htfab/tt-demo-pcb/rp2350.kicad_sch

## KiCad design rp2350.kicad_sch (2025-12-01)

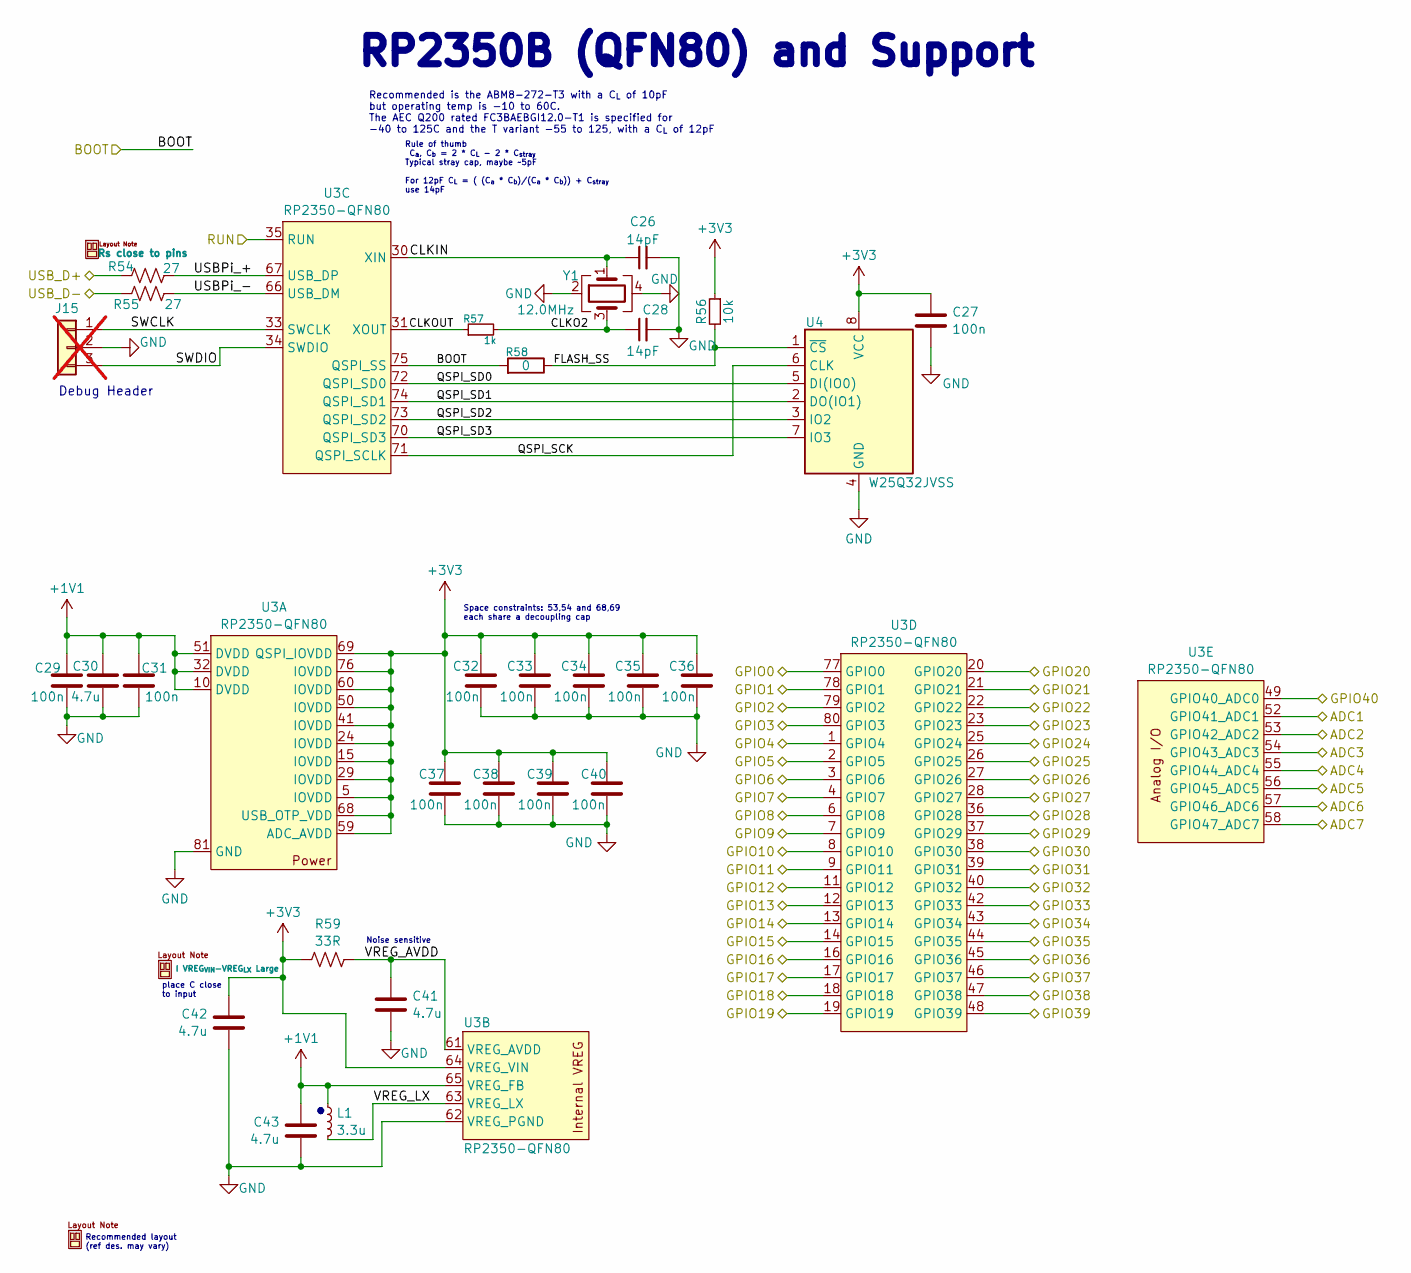
[picture p11: schematic rp2350.kicad_sch]

Parts:
C26, C28: 14pF; C_0402_1005Metric; MPN CC0402CRNPO9BN4R0; LCSC C325455
C27, C29, C31, C32, C33, C34, C35, C36, C37, C38, C39, C40: 100n; C_0402_1005Metric; MPN CL05A104KA5NNNC; LCSC C100072
C30, C41: 4.7u; C_0402_1005Metric; MPN GRM155R61E475ME15D; JLC C2858031
C42, C43: 4.7u; C_0603_1608Metric; MPN GRM188C71C475KE21D; JLC C237615
J15: Conn_01x03; PinHeader_1x03_P2.54mm_Vertical; not fitted
L1: 3.3u; L_2016X120N; MPN AOTA-B201610S3R3-101-T; DigikeyPN 535-AOTA-B201610S3R3-101-TCT-ND
LAYOUT1: Rs close to pins
LAYOUT2: I VREG_{VIN}-VREG_{LX} Large
LAYOUT3: (no value)
R54, R55: 27; R_0402_1005Metric; MPN AF0402FR-0727RL; JLC C2098172
R56: 10k; R_0402_1005Metric; MPN RC0402FR-0710KL; LCSC C471764
R57: 1k; R_0402_1005Metric; MPN CR0402-FX-1001GLF; LCSC C202394
R58: 0; R_0402_1005Metric; MPN RMCF0402ZT0R00; DigikeyPN RMCF0402ZT0R00CT-ND
R59: 33R; R_0402_1005Metric; MPN RCS040233R0FKED; JLC C25105
U3: RP2350-QFN80; QFN-80-1EP_10x10mm_P0.4mm_EP3.4x3.4mm; MPN RP2350B; JLC C42415655
U4: W25Q32JVSS; SOIC-8_5.3x5.3mm_P1.27mm; MPN W25Q32JVSSIQ; JLC C82344
Y1: 12.0MHz; Crystal_SMD_3225-4Pin_3.2x2.5mm; MPN FC3BAEBGI12.0-T1; DigikeyPN 631-FC3BAEBGI12.0-T1CT-ND

Connections:
+1V1: C29.1, C30.1, C31.1, C43.1, L1.1, U3.10 (DVDD), U3.32 (DVDD), U3.51 (DVDD), U3.65 (VREG_FB)
+3V3: C27.1, C32.1, C33.1, C34.1, C35.1, C36.1, C37.1, C38.1, C39.1, C40.1, C42.1, R56.1, R59.1, U3.5 (IOVDD), U3.15 (IOVDD), U3.24 (IOVDD), U3.29 (IOVDD), U3.41 (IOVDD), U3.50 (IOVDD), U3.59 (ADC_AVDD), U3.60 (IOVDD), U3.64 (VREG_VIN), U3.68 (USB_OTP_VDD), U3.69 (QSPI_IOVDD), U3.76 (IOVDD), U4.8 (VCC)
ADC1: U3.52 (GPIO41_ADC1)
ADC2: U3.53 (GPIO42_ADC2)
ADC3: U3.54 (GPIO43_ADC3)
ADC4: U3.55 (GPIO44_ADC4)
ADC5: U3.56 (GPIO45_ADC5)
ADC6: U3.57 (GPIO46_ADC6)
ADC7: U3.58 (GPIO47_ADC7)
BOOT: R58.1, U3.75 (QSPI_SS)
CLKIN: C26.1, U3.30 (XIN), Y1.1
CLKO2: C28.1, R57.2, Y1.3
CLKOUT: R57.1, U3.31 (XOUT)
FLASH_SS: R56.2, R58.2, U4.1 (~CS)
GND: C26.2, C27.2, C28.2, C29.2, C30.2, C31.2, C32.2, C33.2, C34.2, C35.2, C36.2, C37.2, C38.2, C39.2, C40.2, C41.2, C42.2, C43.2, J15.2, U3.62 (VREG_PGND), U3.81 (GND), U4.4 (GND), Y1.2, Y1.4
GPIO0: U3.77 (GPIO0)
GPIO1: U3.78 (GPIO1)
GPIO2: U3.79 (GPIO2)
GPIO3: U3.80 (GPIO3)
GPIO4: U3.1 (GPIO4)
GPIO5: U3.2 (GPIO5)
GPIO6: U3.3 (GPIO6)
GPIO7: U3.4 (GPIO7)
GPIO8: U3.6 (GPIO8)
GPIO9: U3.7 (GPIO9)
GPIO10: U3.8 (GPIO10)
GPIO11: U3.9 (GPIO11)
GPIO12: U3.11 (GPIO12)
GPIO13: U3.12 (GPIO13)
GPIO14: U3.13 (GPIO14)
GPIO15: U3.14 (GPIO15)
GPIO16: U3.16 (GPIO16)
GPIO17: U3.17 (GPIO17)
GPIO18: U3.18 (GPIO18)
GPIO19: U3.19 (GPIO19)
GPIO20: U3.20 (GPIO20)
GPIO21: U3.21 (GPIO21)
GPIO22: U3.22 (GPIO22)
GPIO23: U3.23 (GPIO23)
GPIO24: U3.25 (GPIO24)
GPIO25: U3.26 (GPIO25)
GPIO26: U3.27 (GPIO26)
GPIO27: U3.28 (GPIO27)
GPIO28: U3.36 (GPIO28)
GPIO29: U3.37 (GPIO29)
GPIO30: U3.38 (GPIO30)
GPIO31: U3.39 (GPIO31)
GPIO32: U3.40 (GPIO32)
GPIO33: U3.42 (GPIO33)
GPIO34: U3.43 (GPIO34)
GPIO35: U3.44 (GPIO35)
GPIO36: U3.45 (GPIO36)
GPIO37: U3.46 (GPIO37)
GPIO38: U3.47 (GPIO38)
GPIO39: U3.48 (GPIO39)
GPIO40: U3.49 (GPIO40_ADC0)
QSPI_SCK: U3.71 (QSPI_SCLK), U4.6 (CLK)
QSPI_SD0: U3.72 (QSPI_SD0), U4.5 (DI(IO0))
QSPI_SD1: U3.74 (QSPI_SD1), U4.2 (DO(IO1))
QSPI_SD2: U3.73 (QSPI_SD2), U4.3 (IO2)
QSPI_SD3: U3.70 (QSPI_SD3), U4.7 (IO3)
RUN: U3.35 (RUN)
SWCLK: J15.1, U3.33 (SWCLK)
SWDIO: J15.3, U3.34 (SWDIO)
USBPi_+: R54.2, U3.67 (USB_DP)
USBPi_-: R55.2, U3.66 (USB_DM)
USB_D+: R54.1
USB_D-: R55.1
VREG_AVDD: C41.1, R59.2, U3.61 (VREG_AVDD)
VREG_LX: L1.2, U3.63 (VREG_LX)

Notes on the sheet:
Debug Header
Space constraints: 53,54 and 68,69 each share a decoupling cap
place C close to input
Noise sensitive
RP2350B (QFN80) and Support
Rule of thumb C_{a}, C_{b} = 2 * C_{L} - 2 * C_{stray} Typical stray cap, maybe ~5pF For 12pF C_{L} = ( (C_{a} * C_{b})/(C_{a} * C_{b})) + C_{stray} use 14pF
Recommended layout (ref des. may vary)
Recommended is the ABM8-272-T3 with a C_{L} of 10pF but operating temp is -10 to 60C. The AEC Q200 rated FC3BAEBGI12.0-T1 is specified for -40 to 125C and the T variant -55 to 125, with a C_{L} of 12pF
