htfab/tt-demo-pcb/tinytapeout-demo.kicad_sch

## KiCad design tinytapeout-demo.kicad_sch (2025-12-01)

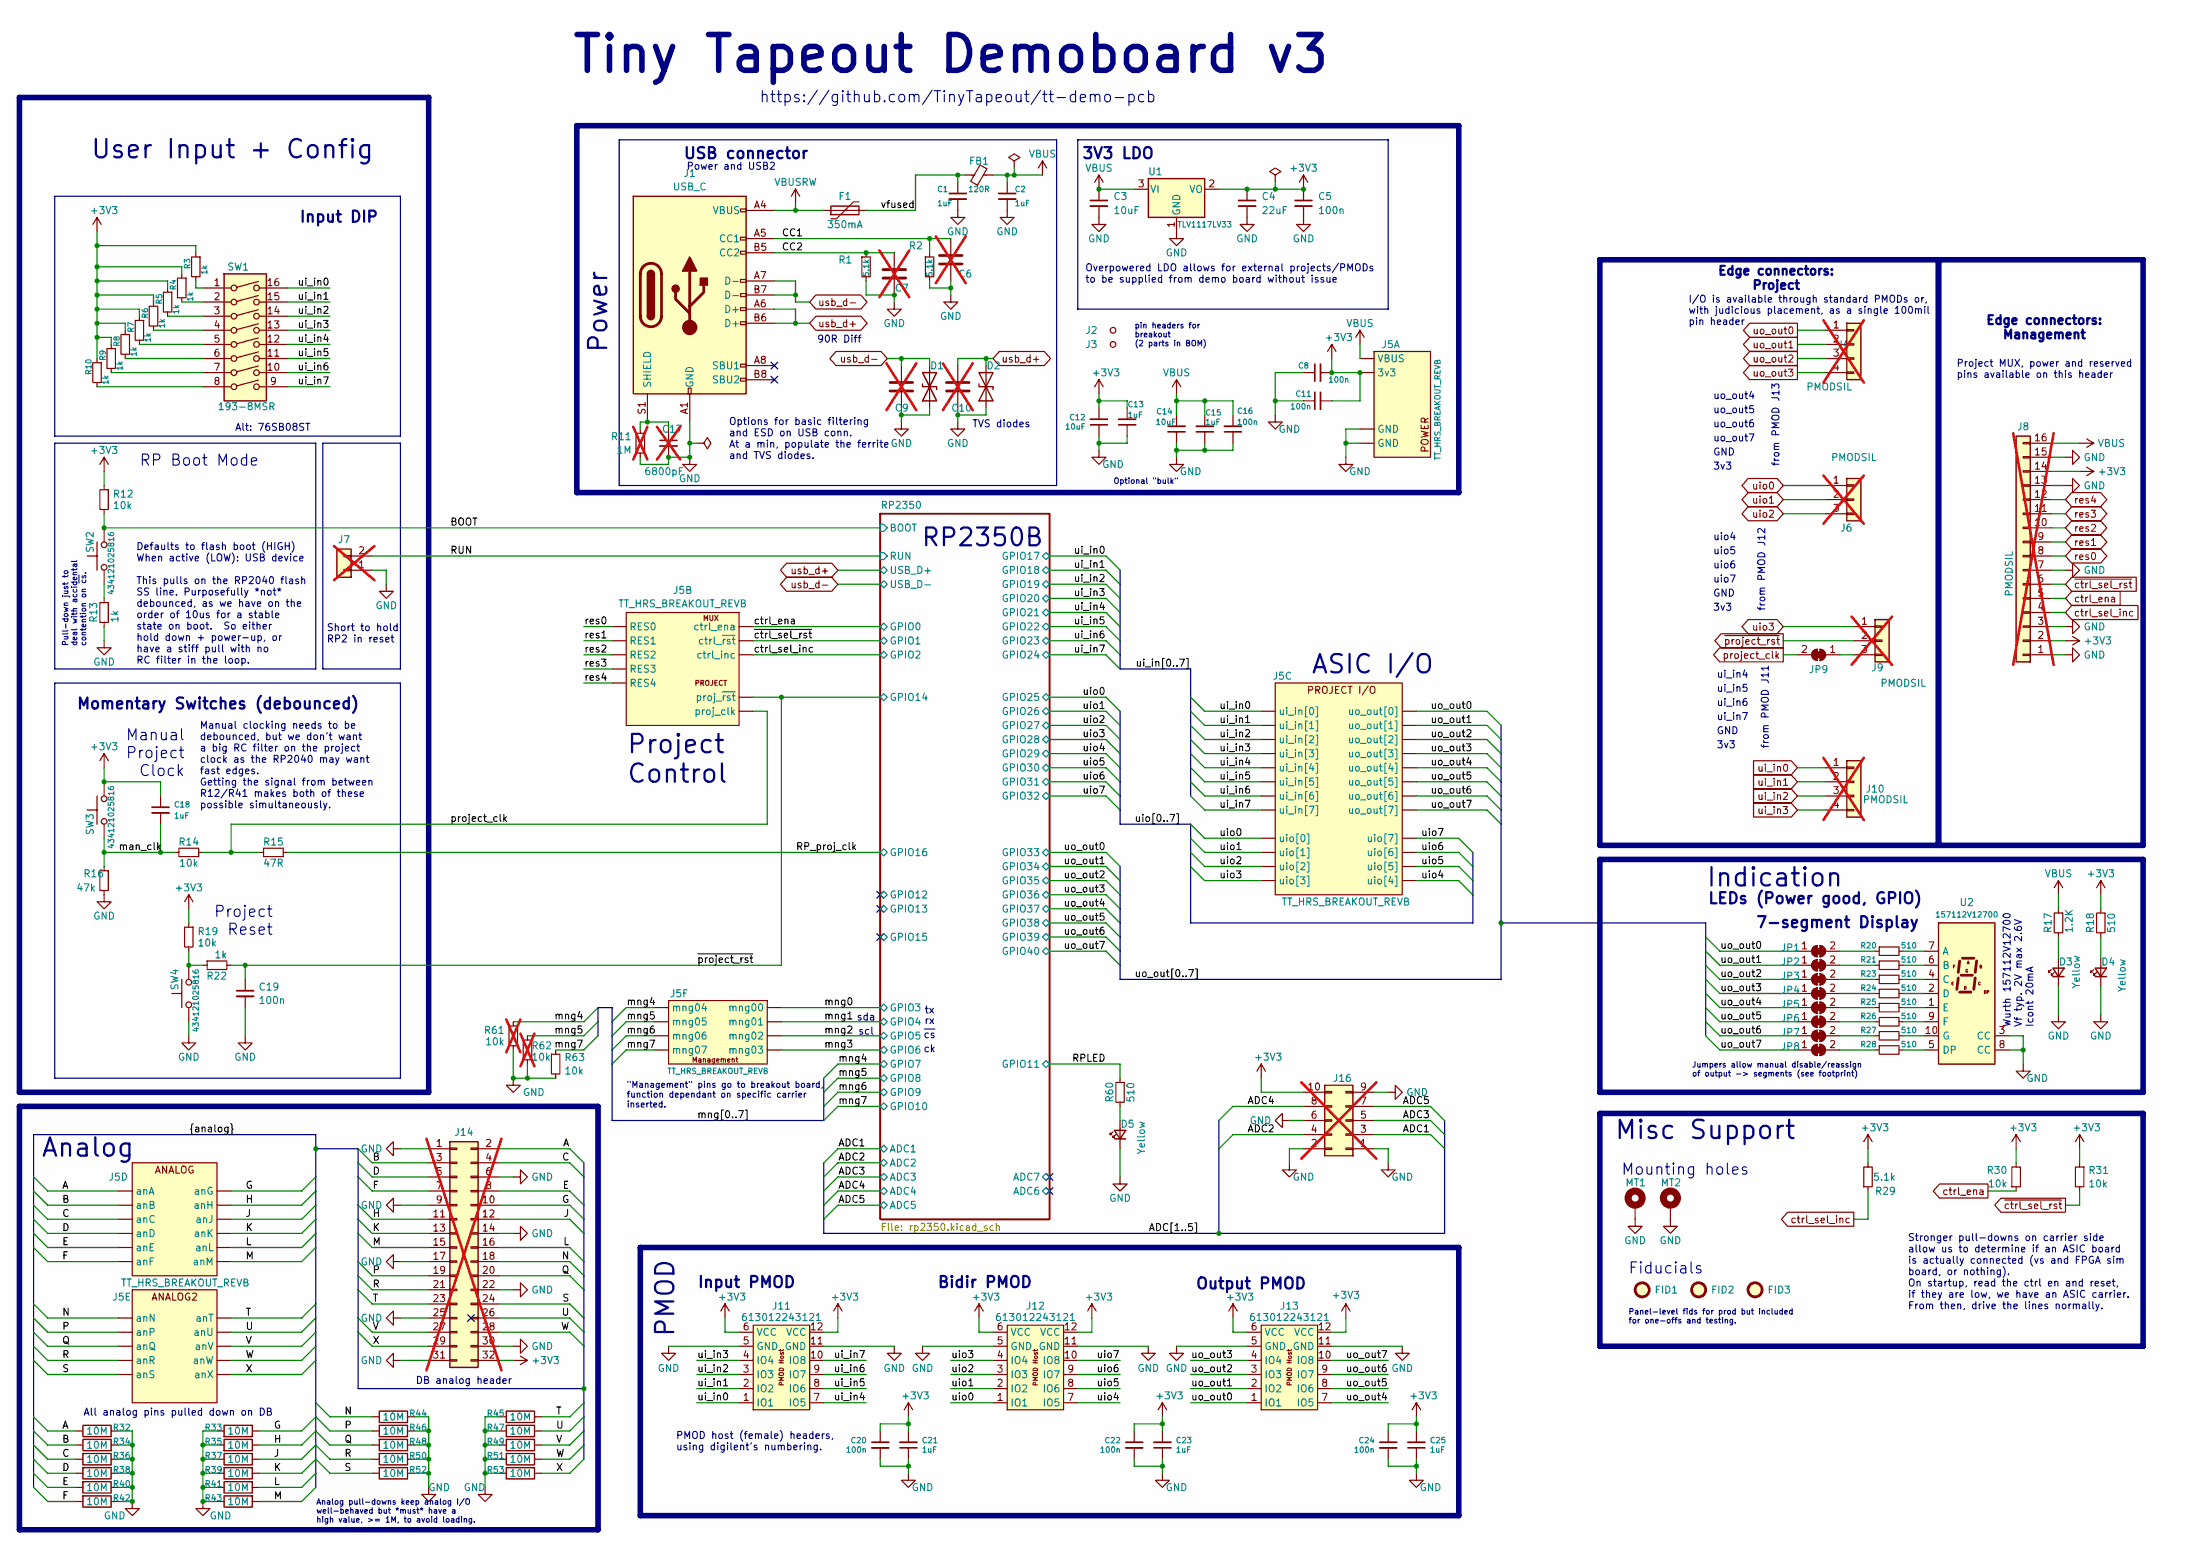
[picture p12: schematic tinytapeout-demo.kicad_sch]

Parts:
C1, C2, C13, C15, C18, C21, C23, C25: 1uF; C_0603_1608Metric; MPN GRM188D72A105KE01D; LCSC C5673
C3, C12, C14: 10uF; C_0805_2012Metric; MPN GRM21BR71C106KE51L; LCSC C408142
C4: 22uF; C_0805_2012Metric; MPN GRT21BR61E226ME13L; LCSC C86816
C5, C8, C11, C16, C19, C20, C22, C24: 100n; C_0402_1005Metric; MPN CL05A104KA5NNNC; LCSC C100072
C6, C7, C9, C10: 33pF; C_0402_1005Metric; MPN CC0402JRNPO9BN330; DigikeyPN 311-1020-1-ND; not fitted
C17: 6800pF; C_0603_1608Metric; MPN GCM188R72A682KA37D; JLC C576423; not fitted
D1, D2: TVS; D_0603_1608Metric; MPN 0603ESDA-AEC1; DigikeyPN 283-0603ESDA-AEC1CT-ND
D3, D4, D5: Yellow; LED_0603_1608Metric; MPN CSL1901YW1; LCSC C72038
F1: 350mA; Fuse_0805_2012Metric; MPN 0ZCK0035FF2G; LCSC C1884490
FB1: 120R; L_0603_1608Metric; MPN MFBM1V1608-121-R; DigikeyPN 283-MFBM1V1608-121-RCT-ND
FID1, FID2, FID3: Fiducial; Fiducial_1mm_Mask2mm
J1: USB_C; USB_C_Receptacle_HRO_TYPE-C-31-M-12; MPN USB-TYPE-C-019; DigikeyPN USB4105-GF-A-120
J2: DF12NB(5.0)-50DP-0.5V(51); TT_BREAKOUT_PINHEADER_PLACEHOLDER_WITHPAD; MPN DF12NB(5.0)-50DP-0.5V(51); JLC C3020266
J3: DF12NB(5.0)-60DP-0.5V(51); TT_BREAKOUT_PINHEADER_PLACEHOLDER_WITHPAD; MPN DF12NB(5.0)-60DP-0.5V(51); JLC C2847989
J4, J10: Conn_01x04; PinHeader_1x04_P2.54mm_Vertical; not fitted
J5: TT_HRS_BREAKOUT_REVB; TT_HRS_CARRIER_REVC
J6, J9: Conn_01x03; PinHeader_1x03_P2.54mm_Vertical; not fitted
J7: Conn_01x02; PinHeader_1x02_P2.54mm_Vertical; not fitted
J8: Conn_01x16; PinHeader_1x16_P2.54mm_Vertical; not fitted
J11, J12, J13: 613012243121; PinSocket_2x06_P2.54mm_PMODHost1A; MPN PPTC062LJBN-RC; LCSC C6147817
J14: Conn_02x16_Odd_Even; PinHeader_2x16_P2.54mm_Vertical; not fitted
J16: Conn_02x05_Odd_Even; PinSocket_2x05_P2.54mm_Vertical; not fitted
JP1, JP2, JP3, JP4, JP5, JP6, JP7, JP8, JP9: SolderJumper_2_Bridged; SolderJumper-2_0603
MT1, MT2: MountingHole_Pad; MountingHole_3.2mm_M3_Pad; MPN DNP
R1, R2, R29: 5.1k; R_0402_1005Metric; MPN AC0402FR-135K1L; LCSC C138073
R3, R4, R5, R6, R7, R8, R9, R10, R13, R22: 1k; R_0402_1005Metric; MPN CR0402-FX-1001GLF; LCSC C202394
R11: 1M; R_0603_1608Metric; LCSC C858907; not fitted
R12, R14, R19, R30, R31, R63: 10k; R_0402_1005Metric; MPN RC0402FR-0710KL; LCSC C471764
R15: 47R; R_0402_1005Metric; MPN RMCF0402JT47R0; LCSC C4271317
R16: 47k; R_0402_1005Metric; MPN RC0402FR-0747KL; JLC C25792
R17: 1.2K; R_0402_1005Metric; MPN RC0402FR-071K2L; LCSC C138040
R18, R20, R21, R23, R24, R25, R26, R27, R28, R60: 510; R_0402_1005Metric; MPN RC0402FR-07510RL; LCSC C276273
R32, R33, R34, R35, R36, R37, R38, R39, R40, R41, R42, R43, R44, R45, R46, R47, R48, R49, R50, R51, R52, R53: 10M; R_0402_1005Metric; MPN CRCW040210M0FKEDC; DigikeyPN YAG3450CT-ND
R61, R62: 10k; R_0402_1005Metric; MPN RC0402FR-0710KL; LCSC C471764; not fitted
SW1: 193-8MSR; GENERIC_PIANO_8DIP; MPN DSPV08LSGET; LCSC C3293170
SW2, SW3, SW4: 434121025816; MPN 434121025816; LCSC C329185
U1: TLV1117LV33; SOT-223-3_TabPin2; MPN TLV1117LV33DCYR; LCSC C15578
U2: 157112V12700; WL_S7DS-157112V12700; MPN 157112V12700; DigikeyPN 732-157112V12700DKR-ND

Connections:
+3V3: C4.1, C5.1, C8.2, C11.2, C12.2, C13.2, C18.1, C20.1, C21.2, C22.1, C23.2, C24.1, C25.2, J5.L1 (3v3), J5.R8 (3v3), J5.R10 (3v3), J8.2, J8.14, J11.6 (VCC), J11.12 (VCC), J12.6 (VCC), J12.12 (VCC), J13.6 (VCC), J13.12 (VCC), J14.32, J16.10, R3.1, R4.1, R5.1, R6.1, R7.1, R8.1, R9.1, R10.1, R12.1, R18.1, R19.1, R29.2, R30.2, R31.1, SW3.2, U1.2 (VO)
A: J5.L2 (an0), J14.2, R32.2
ADC1: J16.3
ADC2: J16.4
ADC3: J16.5
ADC4: J16.8
ADC5: J16.7
B: J5.L4 (an1), J14.3, R34.2
BOOT: R12.2, SW2.2
C: J5.L6 (an2), J14.4, R36.1
CC1: C6.1, J1.A5 (CC1), R2.1
CC2: C7.1, J1.B5 (CC2), R1.1
D: J5.L10 (an3), J14.5, R38.1
E: J5.L12 (an4), J14.8, R40.1
F: J5.L14 (an5), J14.7, R42.1
G: J5.L18 (an6), J14.10, R33.2
GND: C1.2, C2.2, C3.2, C4.2, C5.2, C6.2, C7.2, C8.1, C9.2, C10.2, C11.1, C12.1, C13.1, C14.1, C15.1, C16.1, C17.2, C19.2, C20.2, C21.1, C22.2, C23.1, C24.2, C25.1, D1.1 (A1), D2.1 (A1), D3.1 (K), D4.1 (K), D5.1 (K), J1.A1 (GND), J1.A12 (GND), J1.B1 (GND), J1.B12 (GND), J5.L3 (GND), J5.L8 (GND), J5.L11 (GND), J5.L16 (GND), J5.L19 (GND), J5.L24 (GND), J5.L27 (GND), J5.L32 (GND), J5.L35 (GND), J5.L40 (GND), J5.L43 (GND), J5.L48 (GND), J5.L51 (GND), J5.L55 (GND), J5.L56 (GND), J5.L59 (GND), J5.R1 (GND), J5.R6 (GND), J5.R11 (GND), J5.R12 (GND), J5.R20 (GND), J5.R21 (GND), J5.R28 (GND), J5.R33 (GND), J5.R38 (GND), J5.R41 (GND), J5.R44 (GND), J5.R45 (GND), J5.R48 (GND), J7.1, J8.1, J8.3, J8.7, J8.13, J8.15, J11.5 (GND), J11.11 (GND), J12.5 (GND), J12.11 (GND), J13.5 (GND), J13.11 (GND), J14.1, J14.6, J14.9, J14.14, J14.17, J14.22, J14.25, J14.30, J14.31, J16.1, J16.2, J16.6, J16.9, MT1.1, MT2.1, R1.2, R2.2, R11.2, R13.2, R16.2, R32.1, R33.1, R34.1, R35.1, R36.2, R37.2, R38.2, R39.2, R40.2, R41.2, R42.2, R43.2, R44.1, R45.1, R46.1, R47.1, R48.2, R49.2, R50.2, R51.2, R52.2, R53.2, R61.2, R62.2, R63.2, SW4.1, U1.1 (GND), U2.3 (CC), U2.8 (CC)
H: J5.L20 (an7), J14.11, R35.2
J: J5.L22 (an8), J14.12, R37.1
K: J5.L26 (an9), J14.13, R39.1
L: J5.L28 (an10), J14.16, R41.1
M: J5.L30 (an11), J14.15, R43.1
N: J5.L34 (an12), J14.18, R44.2
unnamed: C17.1, J1.S1 (SHIELD), R11.1
unnamed: D3.2 (A), R17.2
unnamed: D4.2 (A), R18.2
unnamed: D5.2 (A), R60.2
unnamed: J9.3, JP9.1 (A)
unnamed: JP1.2 (B), R20.1
unnamed: JP2.2 (B), R21.1
unnamed: JP3.2 (B), R23.1
unnamed: JP4.2 (B), R24.1
unnamed: JP5.2 (B), R25.1
unnamed: JP6.2 (B), R26.1
unnamed: JP7.2 (B), R27.1
unnamed: JP8.2 (B), R28.1
unnamed: R3.2, SW1.1
unnamed: R4.2, SW1.2
unnamed: R5.2, SW1.3
unnamed: R6.2, SW1.4
unnamed: R7.2, SW1.5
unnamed: R8.2, SW1.6
unnamed: R9.2, SW1.7
unnamed: R10.2, SW1.8
unnamed: R13.1, SW2.1
unnamed: R19.2, R22.1, SW4.2
unnamed: R20.2, U2.7 (A)
unnamed: R21.2, U2.6 (B)
unnamed: R23.2, U2.4 (C)
unnamed: R24.2, U2.2 (D)
unnamed: R25.2, U2.1 (E)
unnamed: R26.2, U2.9 (F)
unnamed: R27.2, U2.10 (G)
unnamed: R28.2, U2.5 (DP)
P: J5.L36 (an13), J14.19, R46.2
Q: J5.L38 (an14), J14.20, R48.1
R: J5.L42 (an15), J14.21, R50.1
RPLED: R60.1
RP_proj_clk: R15.1
RUN: J7.2
S: J5.L44 (an16), J14.24, R52.1
T: J5.L46 (an17), J14.23, R45.2
U: J5.L50 (an18), J14.26, R47.2
V: J5.L52 (an19), J14.27, R49.1
VBUS: C2.1, C3.1, C14.2, C15.2, C16.2, FB1.2, J5.R2 (VBUS), J5.R4 (VBUS), J8.16, R17.1, U1.3 (VI)
VBUSRW: F1.1, J1.A4 (VBUS), J1.A9 (VBUS), J1.B4 (VBUS), J1.B9 (VBUS)
W: J5.L54 (an20), J14.28, R51.1
X: J5.L58 (an21), J14.29, R53.1
ctrl_ena: J5.R46 (ctrl_ena), J8.5, R30.1
ctrl_sel_inc: J5.R47 (ctrl_inc), J8.4, R29.1
man_clk: C18.2, R14.2, R16.1, SW3.1
mng0: J5.R42 (mng00)
mng1: J5.R40 (mng01)
mng2: J5.R36 (mng02)
mng3: J5.R30 (mng03)
mng4: J5.R26 (mng04), R61.1
mng5: J5.R22 (mng05), R62.1
mng6: J5.R18 (mng06)
mng7: J5.R16 (mng07), R63.1
project_clk: J5.L57 (proj_clk), JP9.2 (B), R14.1, R15.2
res0: J5.R39 (RES0), J8.8
res1: J5.R37 (RES1), J8.9
res2: J5.R35 (RES2), J8.10
res3: J5.R31 (RES3), J8.11
res4: J5.R29 (RES4), J8.12
ui_in0: J5.L31 (ui_in[0]), J10.1, J11.1 (IO1), SW1.16
ui_in1: J5.L33 (ui_in[1]), J10.2, J11.2 (IO2), SW1.15
ui_in2: J5.L37 (ui_in[2]), J10.3, J11.3 (IO3), SW1.14
ui_in3: J5.L39 (ui_in[3]), J10.4, J11.4 (IO4), SW1.13
ui_in4: J5.L41 (ui_in[4]), J11.7 (IO5), SW1.12
ui_in5: J5.L45 (ui_in[5]), J11.8 (IO6), SW1.11
ui_in6: J5.L47 (ui_in[6]), J11.9 (IO7), SW1.10
ui_in7: J5.L49 (ui_in[7]), J11.10 (IO8), SW1.9
uio0: J5.L5 (uio[0]), J6.1, J12.1 (IO1)
uio1: J5.L7 (uio[1]), J6.2, J12.2 (IO2)
uio2: J5.L9 (uio[2]), J6.3, J12.3 (IO3)
uio3: J5.L13 (uio[3]), J9.1, J12.4 (IO4)
uio4: J5.L15 (uio[4]), J12.7 (IO5)
uio5: J5.L17 (uio[5]), J12.8 (IO6)
uio6: J5.L21 (uio[6]), J12.9 (IO7)
uio7: J5.L23 (uio[7]), J12.10 (IO8)
uo_out0: J4.1, J5.R19 (uo_out[0]), J13.1 (IO1), JP1.1 (A)
uo_out1: J4.2, J5.R17 (uo_out[1]), J13.2 (IO2), JP2.1 (A)
uo_out2: J4.3, J5.R15 (uo_out[2]), J13.3 (IO3), JP3.1 (A)
uo_out3: J4.4, J5.R13 (uo_out[3]), J13.4 (IO4), JP4.1 (A)
uo_out4: J5.R9 (uo_out[4]), J13.7 (IO5), JP5.1 (A)
uo_out5: J5.R7 (uo_out[5]), J13.8 (IO6), JP6.1 (A)
uo_out6: J5.R5 (uo_out[6]), J13.9 (IO7), JP7.1 (A)
uo_out7: J5.R3 (uo_out[7]), J13.10 (IO8), JP8.1 (A)
usb_d+: C10.1, D2.2 (A2), J1.A6 (D+), J1.B6 (D+)
usb_d-: C9.1, D1.2 (A2), J1.A7 (D-), J1.B7 (D-)
vfused: C1.1, F1.2, FB1.1
~ctrl_sel_rst: J5.R43 (ctrl_~rst), J8.6, R31.2
~project_rst: C19.1, J5.L53 (proj_~rst), J9.2, R22.2

Notes on the sheet:
uo_out5
GND
uo_out4
3v3
PMOD host (female) headers, using digilent's numbering.
All analog pins pulled down on DB
RP2350B
Input DIP
ui_in6
Options for basic filtering and ESD on USB conn. At a min, populate the ferrite and TVS diodes.
uo_out7
Edge connectors: Management
Output PMOD
Pull-down just to deal with accidental contention on ~{cs}.
Manual Project Clock
Mounting holes
LEDs (Power good, GPIO)
Fiducials
uo_out6
Input PMOD
Analog
Power
Project Reset
uio7
DB analog header
Manual clocking needs to be debounced, but we don't want a big RC filter on the project clock as the RP2040 may want fast edges. Getting the signal from between R12/R41 makes both of these possible simultaneously.
ui_in7
7-segment Display
Optional "bulk"
ui_in4
scl
from PMOD J12
Misc Support
User Input + Config
Overpowered LDO allows for external projects/PMODs to be supplied from demo board without issue
Tiny Tapeout Demoboard v3
from PMOD J13
Momentary Switches (debounced)
Indication
Defaults to flash boot (HIGH) When active (LOW): USB device This pulls on the RP2040 flash SS line. Purposefully *not* debounced, as we have on the order of 10us for a stable state on boot. So either hold down + power-up, or have a stiff pull with no RC filter in the loop.
Project Control
90R Diff
Edge connectors: Project
I/O is available through standard PMODs or, with judicious placement, as a single 100mil pin header
ASIC I/O
Jumpers allow manual disable/reassign of output -> segments (see footprint)
pin headers for breakout (2 parts in BOM)
Panel-level fids for prod but included for one-offs and testing.
RP Boot Mode
Wurth 157112V12700 Vf typ. 2V max 2.6V Icont 20mA
Project MUX, power and reserved pins available on this header
Short to hold RP2 in reset
TVS diodes
"Management" pins go to breakout board, function dependant on specific carrier inserted.
Bidir PMOD
USB connector
Analog pull-downs keep analog I/O well-behaved but *must* have a high value, >= 1M, to avoid loading.
Power and USB2
uio4
https://github.com/TinyTapeout/tt-demo-pcb
uio5
uio6
sda
PMOD
3V3 LDO
Stronger pull-downs on carrier side allow us to determine if an ASIC board is actually connected (vs and FPGA sim board, or nothing). On startup, read the ctrl en and reset, if they are low, we have an ASIC carrier. From then, drive the lines normally.
ui_in5
~{cs}
Alt: 76SB08ST
from PMOD J11
